Ultrawipf/t42_stm32/Common/Inc/t42_constants.h

/*
 * t42_constants.h
 *
 *  Created on: May 23, 2025
 *      Author: Yannick
 */

#ifndef INC_T42_CONSTANTS_H_
#define INC_T42_CONSTANTS_H_
#include "main.h"
#define NETPOS 2032
#define NETHEIGHT 522
#define MINDACVAL 50
#define MAXDACVAL 4015
#define FIELDLENGTH 1480

extern const uint16_t fieldX[FIELDLENGTH];
extern const uint16_t fieldY[FIELDLENGTH];



#endif /* INC_T42_CONSTANTS_H_ */
